vincentBenet/keyboard_steamdeck/meca/separator.SLDPRT

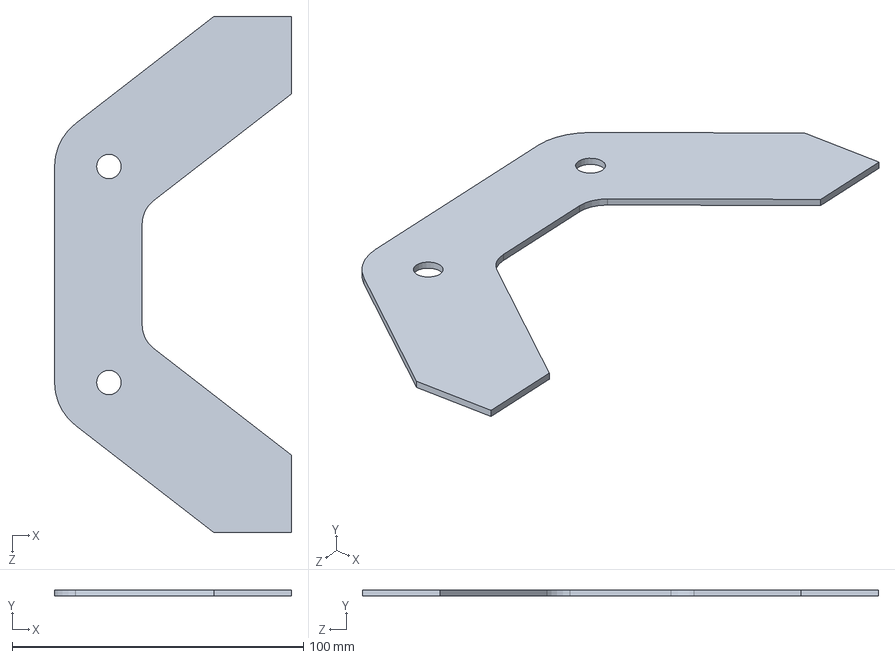
[picture p13: CAD file, 2024-01-31]
meca/separator.SLDPRT
81.4 x 2.00 x 177.2 mm
