vincentBenet/keyboard_steamdeck/mxcap.STEP

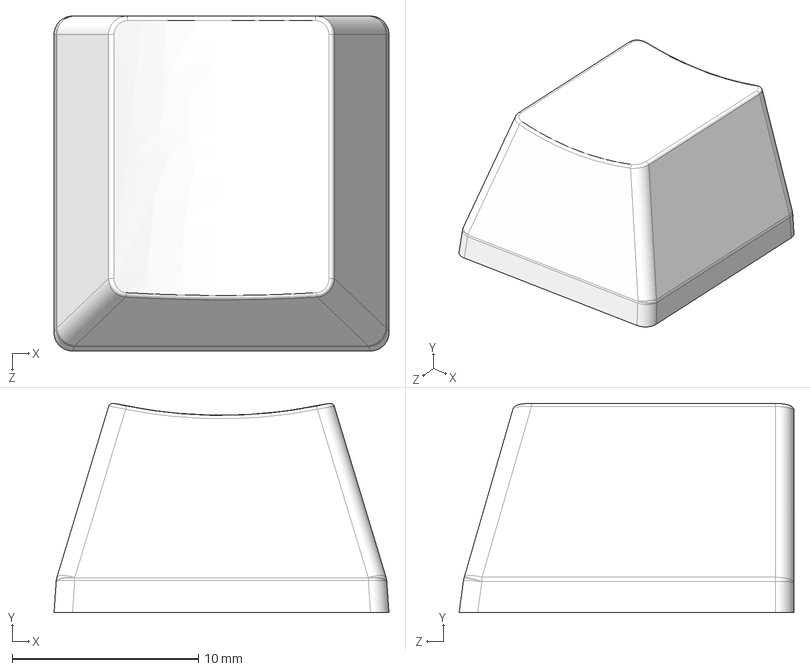
[picture p14: CAD file, 2023-10-10]
mxcap.STEP
18.0 x 11.3 x 18.0 mm
