vincentBenet/keyboard_steamdeck/build/plaque_frontale.DXF

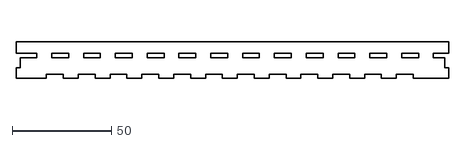
[picture p15: CAD file, 2023-10-13]
build/plaque_frontale.DXF
217.4 x 18.1
