vincentBenet/keyboard_steamdeck/meca/plaque_arriere.SLDPRT

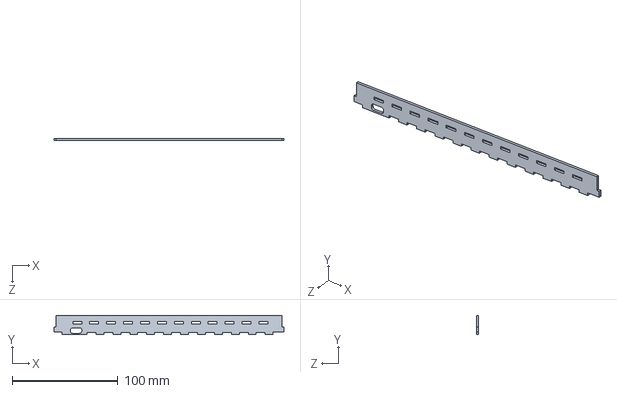
[picture p16: CAD file, 2024-01-31]
meca/plaque_arriere.SLDPRT
217.4 x 18.1 x 2.00 mm
