vincentBenet/keyboard_steamdeck/build/plaque_arriere.DXF

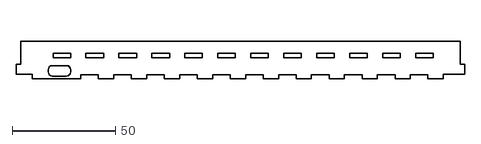
[picture p17: CAD file, 2023-10-13]
build/plaque_arriere.DXF
217.4 x 18.1
