vincentBenet/keyboard_steamdeck/meca/plaque_laterale.SLDPRT

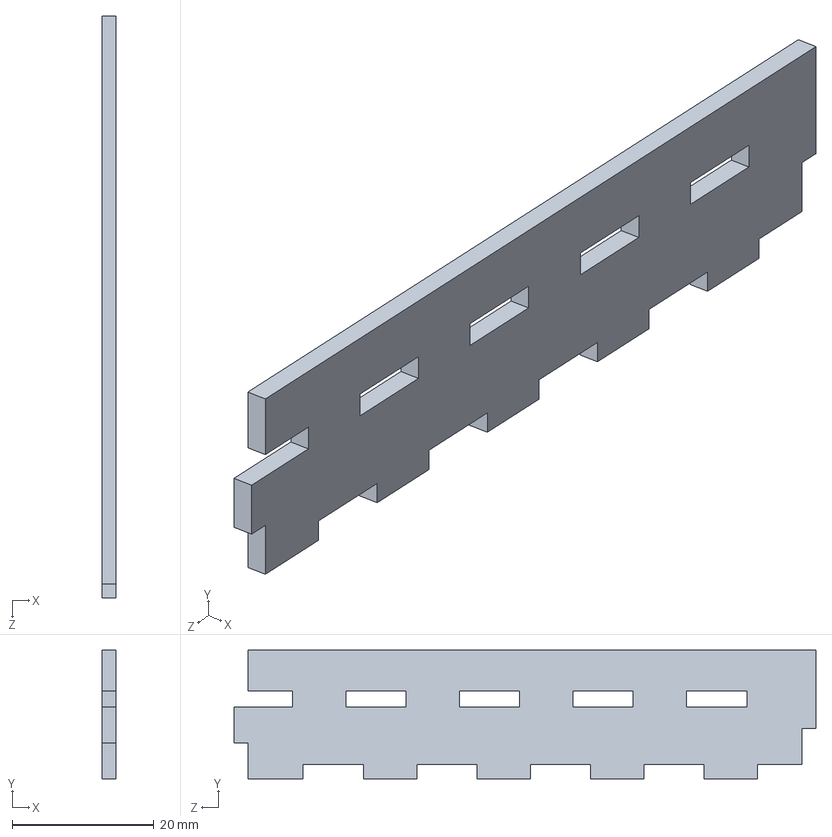
[picture p18: CAD file, 2024-01-31]
meca/plaque_laterale.SLDPRT
2.00 x 18.1 x 82.0 mm
