vincentBenet/keyboard_steamdeck/meca/entretoise.SLDPRT

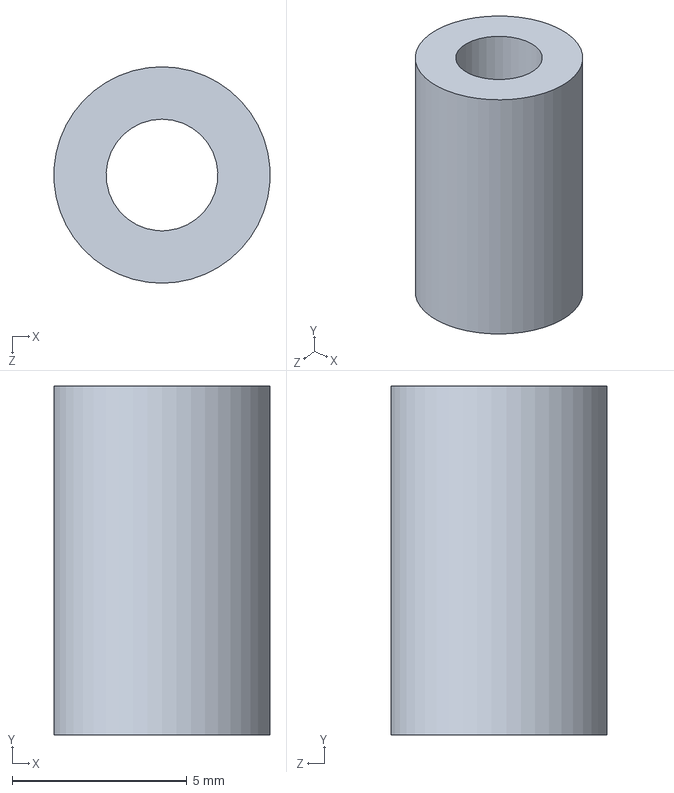
[picture p19: CAD file, 2023-10-11]
meca/entretoise.SLDPRT
6.19 x 10.0 x 6.20 mm
