vincentBenet/keyboard_steamdeck/meca/plaque_principale_pleine.DXF

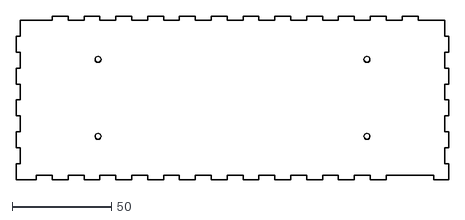
[picture p20: CAD file, 2023-10-11]
meca/plaque_principale_pleine.DXF
217.4 x 82.0
