vincentBenet/keyboard_steamdeck/meca/ecrou_M3.SLDPRT

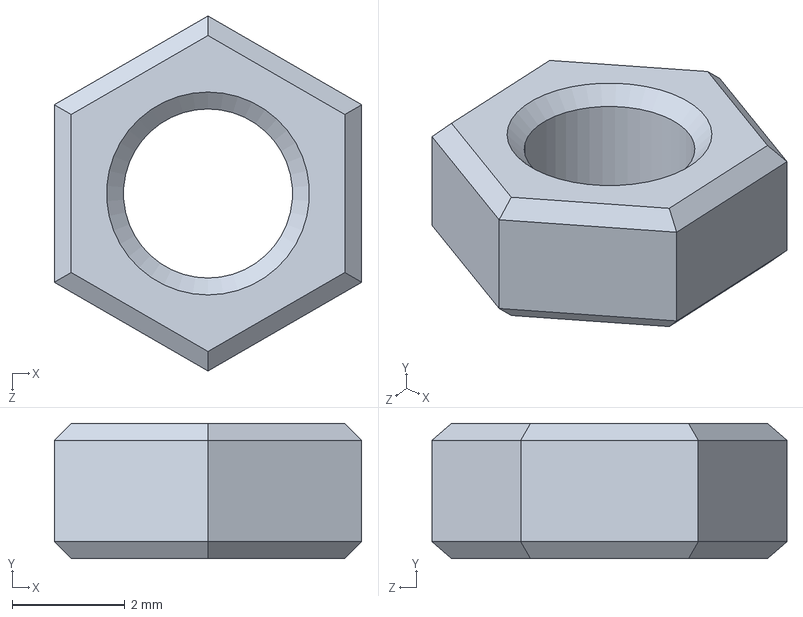
[picture p21: CAD file, 2023-10-10]
meca/ecrou_M3.SLDPRT
5.46 x 2.40 x 6.30 mm
