vincentBenet/keyboard_steamdeck/meca/USB-C and flexed cable.step

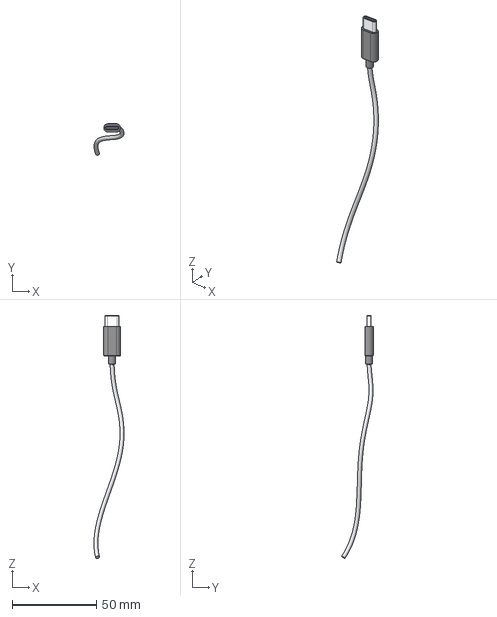
[picture p22: CAD file, 2023-10-10]
meca/USB-C and flexed cable.step
17.9 x 18.8 x 144.6 mm
